dakaneye/word-clock-for-my-daughters/docs/superpowers/plans/2026-07-13-sd-loader.md

# SD Loader Implementation Plan

> **For agentic workers:** REQUIRED SUB-SKILL: Use superpowers:subagent-driven-development (recommended) or superpowers:executing-plans to implement this plan task-by-task. Steps use checkbox (`- [ ]`) syntax for tracking.

**Goal:** One command that loads/updates the three audio WAVs on the SD card inside a closed clock over the captive USB cable + WiFi, then restores the exact firmware image that was running.

**Architecture:** A standalone loader firmware (`firmware/tools/sd_loader/`) mounts the SD, joins WiFi (NVS creds or serial-supplied), and executes line-based serial commands to pull files from a temporary HTTP server on the Mac. A host orchestrator (`firmware/tools/sd_load.py`) stages/converts audio, dumps the clock's full flash with esptool, flashes the loader, drives the transfer, then writes the dump back. Pure logic lives in `sd_load_core.py` (pytest-covered, importable without pyserial/esptool).

**Tech Stack:** PlatformIO (espressif32@6.8.0, Arduino), Python 3 stdlib (+pyserial), esptool (PlatformIO-bundled 4.5), afconvert (macOS built-in).

**Spec:** `docs/superpowers/specs/2026-07-13-sd-loader-design.md`

## Global Constraints

- Loader firmware pins `platform = espressif32@6.8.0` (exact, no caret) and `build_unflags = -std=gnu++11` — both load-bearing (CLAUDE.md).
- `board = esp32dev`, `monitor_speed = 115200`, serial protocol at 115200.
- Canonical SD filenames: `lullaby1.wav`, `lullaby2.wav`, `birth.wav` at FAT32 root. WAV format: RIFF/WAVE, PCM (format 1), mono, 44100 Hz, 16-bit.
- CRC32 = zlib polynomial (0xEDB88320), init 0, both sides.
- Serial protocol fields are TAB-separated (SSIDs/passwords may contain spaces).
- pio at `~/Library/Python/3.9/bin/pio`; esptool at `~/.platformio/packages/tool-esptoolpy/esptool.py`.
- Conventional commits, no attribution trailers. All commands below run from `firmware/`.
- The clone CP2102 replays stale serial data: every fresh capture uses reset-hold → flush → release (see `tools/bench_acceptance.py` `Board.reset_and_capture`).

---

### Task 1: Host pure-logic core

**Files:**
- Create: `firmware/tools/sd_load_core.py`
- Test: `firmware/tools/test_sd_load_core.py`

**Interfaces:**
- Produces (used by Task 3):
  - `validate_wav(path: Path) -> int` — returns data-chunk byte size; raises `ValueError` with a human reason on any spec violation
  - `file_crc32(path: Path) -> int`
  - `afconvert_cmd(src: Path, dst: Path) -> list[str]`
  - `resolve_inputs(args) -> dict[str, Path]` — maps slot name (`lullaby1.wav` etc.) → source file; raises `ValueError` if nothing resolves
  - `format_get(url: str, name: str, size: int, crc: int) -> str` — the `G` line
  - `parse_line(line: str) -> dict` — `{"kind": "ready"|"ok"|"err"|"file"|"prog"|"noise", ...fields}`
  - `backup_name(now: datetime) -> str` — `flash-YYYYMMDD-HHMMSS.bin`

- [ ] **Step 1: Write the failing tests**

```python
# firmware/tools/test_sd_load_core.py
import struct
import zlib
from datetime import datetime
from pathlib import Path

import pytest

import sd_load_core as core

def make_wav(path: Path, *, channels=1, rate=44100, bits=16,
             fmt=1, data=b"\x00\x01" * 100, magic=b"RIFF", wave=b"WAVE"):
    """Minimal RIFF/WAVE writer for tests."""
    fmt_chunk = struct.pack("<4sIHHIIHH", b"fmt ", 16, fmt, channels,
                            rate, rate * channels * bits // 8,
                            channels * bits // 8, bits)
    data_chunk = struct.pack("<4sI", b"data", len(data)) + data
    body = wave + fmt_chunk + data_chunk
    path.write_bytes(magic + struct.pack("<I", len(body)) + body)
    return path

def test_validate_wav_accepts_spec_file(tmp_path):
    p = make_wav(tmp_path / "ok.wav")
    assert core.validate_wav(p) == 200

@pytest.mark.parametrize("kwargs,needle", [
    ({"channels": 2}, "mono"),
    ({"rate": 48000}, "44100"),
    ({"bits": 24}, "16-bit"),
    ({"fmt": 3}, "PCM"),
    ({"magic": b"RIFX"}, "RIFF"),
    ({"data": b""}, "empty"),
])
def test_validate_wav_rejects_violations(tmp_path, kwargs, needle):
    p = make_wav(tmp_path / "bad.wav", **kwargs)
    with pytest.raises(ValueError, match=needle):
        core.validate_wav(p)

def test_file_crc32_matches_zlib(tmp_path):
    p = tmp_path / "f.bin"
    p.write_bytes(b"hello sd loader")
    assert core.file_crc32(p) == zlib.crc32(b"hello sd loader")

def test_afconvert_cmd_shape(tmp_path):
    cmd = core.afconvert_cmd(Path("in.m4a"), Path("out.wav"))
    assert cmd[0] == "afconvert"
    assert "-d" in cmd and "LEI16@44100" in cmd
    assert "-c" in cmd and "1" in cmd
    assert cmd[-2:] == ["in.m4a", "out.wav"]

def test_resolve_inputs_from_flags(tmp_path):
    a = make_wav(tmp_path / "a.wav")
    got = core.resolve_inputs(
        type("A", (), {"lullaby1": a, "lullaby2": None, "birth": None,
                       "directory": None})())
    assert got == {"lullaby1.wav": a}

def test_resolve_inputs_from_directory(tmp_path):
    l1 = make_wav(tmp_path / "lullaby1.m4a")
    b = make_wav(tmp_path / "birth.wav")
    got = core.resolve_inputs(
        type("A", (), {"lullaby1": None, "lullaby2": None, "birth": None,
                       "directory": tmp_path})())
    assert got == {"lullaby1.wav": l1, "birth.wav": b}

def test_resolve_inputs_empty_raises(tmp_path):
    with pytest.raises(ValueError, match="[Nn]o input"):
        core.resolve_inputs(
            type("A", (), {"lullaby1": None, "lullaby2": None,
                           "birth": None, "directory": tmp_path})())

def test_format_get_is_tab_separated():
    line = core.format_get("http://10.0.0.5:8123/birth.wav",
                           "birth.wav", 12345, 0xDEADBEEF)
    assert line == ("G http://10.0.0.5:8123/birth.wav\tbirth.wav"
                    "\t12345\tdeadbeef\n")

@pytest.mark.parametrize("line,kind,extra", [
    ("READY sd=ok wifi=192.168.1.44", "ready",
     {"sd": "ok", "wifi": "192.168.1.44"}),
    ("READY sd=fail wifi=none", "ready", {"sd": "fail", "wifi": "none"}),
    ("OK got birth.wav 12345 deadbeef", "ok", {}),
    ("ERR get http 404", "err", {}),
    ("FILE lullaby1.wav 10485760 0012abcd", "file",
     {"name": "lullaby1.wav", "size": 10485760, "crc": 0x0012ABCD}),
    ("PROG birth.wav 45", "prog", {"name": "birth.wav", "pct": 45}),
    ("[boot] anything else", "noise", {}),
])
def test_parse_line(line, kind, extra):
    got = core.parse_line(line)
    assert got["kind"] == kind
    for k, v in extra.items():
        assert got[k] == v

def test_backup_name():
    assert core.backup_name(datetime(2026, 7, 13, 9, 5, 7)) == \
        "flash-20260713-090507.bin"
```

- [ ] **Step 2: Run tests to verify they fail**

Run: `cd firmware/tools && python3 -m pytest test_sd_load_core.py -q`
Expected: collection error — `ModuleNotFoundError: No module named 'sd_load_core'`

- [ ] **Step 3: Write the implementation**

```python
# firmware/tools/sd_load_core.py
"""Pure logic for sd_load.py — importable without pyserial/esptool.

WAV validation, CRC, input resolution, and the serial protocol's line
formats. The wire protocol is defined in
docs/superpowers/specs/2026-07-13-sd-loader-design.md.
"""
import re
import struct
import zlib
from datetime import datetime
from pathlib import Path

SLOTS = ("lullaby1.wav", "lullaby2.wav", "birth.wav")

def validate_wav(path: Path) -> int:
    """Return the data-chunk size of a spec-compliant WAV; raise
    ValueError naming the first violation. Spec: RIFF/WAVE, PCM,
    mono, 44100 Hz, 16-bit, non-empty data."""
    raw = Path(path).read_bytes()
    if len(raw) < 44 or raw[0:4] != b"RIFF" or raw[8:12] != b"WAVE":
        raise ValueError(f"{path.name}: not a RIFF/WAVE file")
    pos, fmt_seen, data_size = 12, False, None
    while pos + 8 <= len(raw):
        cid, csize = raw[pos:pos + 4], struct.unpack_from("<I", raw, pos + 4)[0]
        body = raw[pos + 8:pos + 8 + csize]
        if cid == b"fmt ":
            fmt_seen = True
            fmt, ch, rate, _, _, bits = struct.unpack_from("<HHIIHH", body)
            if fmt != 1:
                raise ValueError(f"{path.name}: not PCM (format {fmt})")
            if ch != 1:
                raise ValueError(f"{path.name}: {ch} channels — must be mono")
            if rate != 44100:
                raise ValueError(f"{path.name}: {rate} Hz — must be 44100")
            if bits != 16:
                raise ValueError(f"{path.name}: {bits}-bit — must be 16-bit")
        elif cid == b"data":
            data_size = csize
        pos += 8 + csize + (csize & 1)   # chunks are word-aligned
    if not fmt_seen:
        raise ValueError(f"{path.name}: missing fmt chunk")
    if not data_size:
        raise ValueError(f"{path.name}: empty data chunk")
    return data_size

def file_crc32(path: Path) -> int:
    crc = 0
    with open(path, "rb") as f:
        while chunk := f.read(65536):
            crc = zlib.crc32(chunk, crc)
    return crc

def afconvert_cmd(src: Path, dst: Path) -> list:
    return ["afconvert", "-f", "WAVE", "-d", "LEI16@44100", "-c", "1",
            str(src), str(dst)]

def resolve_inputs(args) -> dict:
    """Map canonical slot names to source paths from --lullaby1/2/--birth
    flags or a directory of files named <slot-stem>.*  (≥1 required)."""
    out = {}
    for slot in SLOTS:
        stem = slot.split(".")[0]           # lullaby1 / lullaby2 / birth
        flag = getattr(args, stem, None)
        if flag:
            out[slot] = Path(flag)
    if not out and getattr(args, "directory", None):
        d = Path(args.directory)
        for slot in SLOTS:
            stem = slot.split(".")[0]
            hits = sorted(d.glob(f"{stem}.*"))
            if hits:
                out[slot] = hits[0]
    if not out:
        raise ValueError(
            "no inputs: pass --lullaby1/--lullaby2/--birth or a directory "
            f"containing files named {', '.join(s.split('.')[0] + '.*' for s in SLOTS)}")
    return out

def format_get(url: str, name: str, size: int, crc: int) -> str:
    return f"G {url}\t{name}\t{size}\t{crc:08x}\n"

_READY = re.compile(r"^READY sd=(\w+) wifi=(\S+)$")
_FILE = re.compile(r"^FILE (\S+) (\d+) ([0-9a-fA-F]{8})$")
_PROG = re.compile(r"^PROG (\S+) (\d+)$")

def parse_line(line: str) -> dict:
    line = line.strip()
    if m := _READY.match(line):
        return {"kind": "ready", "sd": m.group(1), "wifi": m.group(2)}
    if line.startswith("OK "):
        return {"kind": "ok", "detail": line[3:]}
    if line.startswith("ERR "):
        return {"kind": "err", "detail": line[4:]}
    if m := _FILE.match(line):
        return {"kind": "file", "name": m.group(1),
                "size": int(m.group(2)), "crc": int(m.group(3), 16)}
    if m := _PROG.match(line):
        return {"kind": "prog", "name": m.group(1), "pct": int(m.group(2))}
    return {"kind": "noise", "detail": line}

def backup_name(now: datetime) -> str:
    return now.strftime("flash-%Y%m%d-%H%M%S.bin")
```

- [ ] **Step 4: Run tests to verify they pass**

Run: `cd firmware/tools && python3 -m pytest test_sd_load_core.py -q`
Expected: all pass.

- [ ] **Step 5: Commit**

```bash
git add tools/sd_load_core.py tools/test_sd_load_core.py
git commit -m "feat(tools): sd loader host core logic"
```

---

### Task 2: Loader firmware

**Files:**
- Create: `firmware/tools/sd_loader/platformio.ini`
- Create: `firmware/tools/sd_loader/src/main.cpp`

**Interfaces:**
- Consumes: `configs/pinmap.h` (`PIN_SD_CS`), NVS namespace `wifi`
  (`ssid`/`pw`/`valid` keys — same schema as `nvs_store.cpp`)
- Produces: the serial protocol Task 3 drives (`READY`/`OK`/`ERR`/`FILE`/`PROG` lines; `W`/`G`/`L`/`D` commands per the spec)

- [ ] **Step 1: Write `platformio.ini`**

```ini
; firmware/tools/sd_loader/platformio.ini
; Standalone loader project — see
; docs/superpowers/specs/2026-07-13-sd-loader-design.md.
; Platform pin + build_unflags are load-bearing (CLAUDE.md): 6.8.0 exact,
; and Arduino-ESP32 appends -std=gnu++11 after ours without the unflag.
[env:sdloader]
platform = espressif32@6.8.0
framework = arduino
board = esp32dev
monitor_speed = 115200
build_unflags = -std=gnu++11
build_flags =
    -std=gnu++17
    -Wall
    -Wextra
    -I ../../configs
```

- [ ] **Step 2: Write the loader firmware**

```cpp
// firmware/tools/sd_loader/src/main.cpp
//
// SD LOADER — temporary firmware for cable-only SD content updates on a
// sealed clock. Flashed by tools/sd_load.py, which restores the original
// flash image afterwards. Serves line-based serial commands at 115200:
//
//   W <ssid>\t<pass>                join WiFi with explicit credentials
//   G <url>\t<name>\t<size>\t<crc>  download url -> /<name> (atomic)
//   L                               list SD root (name, size, crc32)
//   D <name>                        delete /<name>
//
// Protocol spec: docs/superpowers/specs/2026-07-13-sd-loader-design.md.
// Reads the clock's stored WiFi credentials from NVS (namespace "wifi",
// same schema as lib/wifi_provision/src/nvs_store.cpp). NEVER writes NVS.
#include <Arduino.h>
#include <HTTPClient.h>
#include <Preferences.h>
#include <SD.h>
#include <WiFi.h>
#include "pinmap.h"

static bool sd_ok = false;

// ---- CRC32 (zlib polynomial, init 0) --------------------------------
static uint32_t crc_table[256];

static void crc_init() {
    for (uint32_t i = 0; i < 256; ++i) {
        uint32_t c = i;
        for (int k = 0; k < 8; ++k)
            c = (c & 1) ? (0xEDB88320UL ^ (c >> 1)) : (c >> 1);
        crc_table[i] = c;
    }
}

// zlib-style: pass the previous return value back in (start with 0).
static uint32_t crc_update(uint32_t crc, const uint8_t* buf, size_t len) {
    crc ^= 0xFFFFFFFFUL;
    for (size_t i = 0; i < len; ++i)
        crc = crc_table[(crc ^ buf[i]) & 0xFF] ^ (crc >> 8);
    return crc ^ 0xFFFFFFFFUL;
}

static uint32_t crc_of_file(const char* path) {
    File f = SD.open(path, FILE_READ);
    if (!f) return 0;
    static uint8_t buf[4096];
    uint32_t crc = 0;
    while (true) {
        int n = f.read(buf, sizeof(buf));
        if (n <= 0) break;
        crc = crc_update(crc, buf, (size_t)n);
    }
    f.close();
    return crc;
}

// ---- WiFi ------------------------------------------------------------
static bool wifi_join(const String& ssid, const String& pw,
                      uint32_t timeout_ms = 20000) {
    WiFi.mode(WIFI_STA);
    WiFi.begin(ssid.c_str(), pw.c_str());
    uint32_t start = millis();
    while (WiFi.status() != WL_CONNECTED) {
        if (millis() - start > timeout_ms) return false;
        delay(100);
    }
    return true;
}

static bool wifi_from_nvs() {
    Preferences p;
    if (!p.begin("wifi", /*readOnly=*/true)) return false;
    bool valid = p.getUChar("valid", 0) == 1;
    String ssid = p.getString("ssid", "");
    String pw = p.getString("pw", "");
    p.end();
    if (!valid || ssid.isEmpty()) return false;
    return wifi_join(ssid, pw);
}

// ---- Commands --------------------------------------------------------
// Split a tab-separated tail into at most n parts (last part keeps tabs).
static int split_tabs(String tail, String* out, int n) {
    int count = 0;
    while (count < n - 1) {
        int t = tail.indexOf('\t');
        if (t < 0) break;
        out[count++] = tail.substring(0, t);
        tail = tail.substring(t + 1);
    }
    out[count++] = tail;
    return count;
}

static void cmd_get(const String& tail) {
    String part[4];
    if (split_tabs(tail, part, 4) != 4) {
        Serial.println("ERR get expected url\\tname\\tsize\\tcrc");
        return;
    }
    const String& url = part[0];
    const String name = "/" + part[1];
    const String temp = name + ".part";
    const uint32_t want_size = strtoul(part[2].c_str(), nullptr, 10);
    const uint32_t want_crc = strtoul(part[3].c_str(), nullptr, 16);

    if (WiFi.status() != WL_CONNECTED) {
        Serial.println("ERR get wifi not connected");
        return;
    }
    HTTPClient http;
    http.setTimeout(15000);
    if (!http.begin(url)) {
        Serial.println("ERR get bad url");
        return;
    }
    int code = http.GET();
    if (code != 200) {
        Serial.printf("ERR get http %d\n", code);
        http.end();
        return;
    }
    SD.remove(temp);
    File out = SD.open(temp, FILE_WRITE);
    if (!out) {
        Serial.println("ERR get sd open failed");
        http.end();
        return;
    }
    WiFiClient* stream = http.getStreamPtr();
    static uint8_t buf[4096];
    uint32_t got = 0, crc = 0, last_pct = 0;
    bool io_fail = false;
    while (got < want_size) {
        size_t want = min((uint32_t)sizeof(buf), want_size - got);
        int n = stream->readBytes(buf, want);   // blocks up to timeout
        if (n <= 0) break;                       // stalled / closed early
        if (out.write(buf, (size_t)n) != (size_t)n) {
            io_fail = true;
            break;
        }
        crc = crc_update(crc, buf, (size_t)n);
        got += (uint32_t)n;
        uint32_t pct = (uint32_t)((uint64_t)got * 100 / want_size);
        if (pct >= last_pct + 5) {
            Serial.printf("PROG %s %u\n", part[1].c_str(), (unsigned)pct);
            last_pct = pct;
        }
    }
    out.close();
    http.end();
    if (io_fail || got != want_size) {
        SD.remove(temp);
        Serial.printf("ERR get short transfer %u/%u%s\n", (unsigned)got,
                      (unsigned)want_size, io_fail ? " (sd write)" : "");
        return;
    }
    if (crc != want_crc) {
        SD.remove(temp);
        Serial.println("ERR get stream crc mismatch");
        return;
    }
    // Read back from the card — proves the bytes that LANDED are right.
    uint32_t disk_crc = crc_of_file(temp.c_str());
    if (disk_crc != want_crc) {
        SD.remove(temp);
        Serial.println("ERR get readback crc mismatch");
        return;
    }
    SD.remove(name);
    if (!SD.rename(temp, name)) {
        Serial.println("ERR get rename failed");
        return;
    }
    Serial.printf("OK got %s %u %08x\n", part[1].c_str(),
                  (unsigned)want_size, (unsigned)want_crc);
}

static void cmd_list() {
    File root = SD.open("/");
    if (!root) {
        Serial.println("ERR list sd root");
        return;
    }
    for (File f = root.openNextFile(); f; f = root.openNextFile()) {
        if (!f.isDirectory()) {
            String path = String("/") + f.name();
            uint32_t size = f.size();
            f.close();
            Serial.printf("FILE %s %u %08x\n", path.c_str() + 1,
                          (unsigned)size,
                          (unsigned)crc_of_file(path.c_str()));
        } else {
            f.close();
        }
    }
    root.close();
    Serial.println("OK list");
}

static void handle(const String& line) {
    if (line.startsWith("W ")) {
        String part[2];
        if (split_tabs(line.substring(2), part, 2) != 2) {
            Serial.println("ERR wifi expected ssid\\tpass");
        } else if (wifi_join(part[0], part[1])) {
            Serial.printf("OK wifi %s\n", WiFi.localIP().toString().c_str());
        } else {
            Serial.println("ERR wifi join failed");
        }
    } else if (line.startsWith("G ")) {
        cmd_get(line.substring(2));
    } else if (line == "L") {
        cmd_list();
    } else if (line.startsWith("D ")) {
        String name = "/" + line.substring(2);
        if (SD.remove(name)) Serial.printf("OK del %s\n", name.c_str() + 1);
        else Serial.printf("ERR del %s\n", name.c_str() + 1);
    } else if (line.length() > 0) {
        Serial.println("ERR unknown command");
    }
}

void setup() {
    Serial.begin(115200);
    crc_init();
    sd_ok = SD.begin(PIN_SD_CS);
    bool wifi = wifi_from_nvs();
    Serial.printf("READY sd=%s wifi=%s\n", sd_ok ? "ok" : "fail",
                  wifi ? WiFi.localIP().toString().c_str() : "none");
}

void loop() {
    static String line;
    while (Serial.available()) {
        char c = (char)Serial.read();
        if (c == '\n') {
            line.trim();
            handle(line);
            line = "";
        } else {
            line += c;
        }
    }
    delay(2);
}
```

- [ ] **Step 3: Compile**

Run: `~/Library/Python/3.9/bin/pio run -d tools/sd_loader`
Expected: `[SUCCESS]`. If `pinmap.h` is not found, the include path is
wrong — it must resolve `firmware/configs/` from `firmware/tools/sd_loader/`
(`-I ../../configs`).

- [ ] **Step 4: Add the build directory to gitignore**

Append to the repo root `.gitignore`:

```
firmware/tools/sd_loader/.pio/
firmware/tools/.flash_backups/
```

- [ ] **Step 5: Commit**

```bash
git add tools/sd_loader/platformio.ini tools/sd_loader/src/main.cpp ../.gitignore
git commit -m "feat(tools): sd loader firmware"
```

---

### Task 3: Host orchestrator

**Files:**
- Create: `firmware/tools/sd_load.py`

**Interfaces:**
- Consumes (from Task 1): `validate_wav`, `file_crc32`, `afconvert_cmd`, `resolve_inputs`, `format_get`, `parse_line`, `backup_name`, `SLOTS`
- Consumes (from Task 2): the loader serial protocol
- Produces: the user-facing command (`sd_load.py [dir] [--lullaby1/--lullaby2/--birth] [--dry-run] [--restore-only BIN] [--port]`)

- [ ] **Step 1: Write the orchestrator**

```python
#!/usr/bin/env python3
"""Load/update the clock's SD audio over the captive USB cable.

Stages (each a hard gate, all narrated):
  1 stage    convert inputs to spec WAVs (afconvert), validate, CRC
  2 backup   esptool read_flash of the ENTIRE flash to tools/.flash_backups/
  3 load     flash the loader firmware, serve staged files over HTTP,
             drive the serial protocol until every CRC matches
  4 restore  esptool write_flash the backup back, verify boot markers

If anything fails after the loader is flashed, the tool attempts the
restore automatically and, failing that, prints the exact
--restore-only recovery command. Design:
docs/superpowers/specs/2026-07-13-sd-loader-design.md
"""
import argparse
import functools
import http.server
import math
import re
import shutil
import socket
import struct
import subprocess
import sys
import tempfile
import threading
import time
import wave
from datetime import datetime, timezone
from pathlib import Path

import serial

import sd_load_core as core

TOOLS = Path(__file__).resolve().parent
FIRMWARE = TOOLS.parent
LOADER = TOOLS / "sd_loader"
BACKUPS = TOOLS / ".flash_backups"
PIO = Path.home() / "Library/Python/3.9/bin/pio"
ESPTOOL = Path.home() / ".platformio/packages/tool-esptoolpy/esptool.py"
BAUDS = (921600, 460800, 115200)
PORT_DEFAULT = "/dev/cu.usbserial-0001"

def say(msg):
    print(f"== {msg}", flush=True)

def run(cmd, **kw):
    print(f"   $ {' '.join(str(c) for c in cmd)}", flush=True)
    return subprocess.run([str(c) for c in cmd], check=True, **kw)

def esptool(port, args, capture=False):
    """Run esptool with baud fallback (clone CP2102 flakes at high baud)."""
    last = None
    for baud in BAUDS:
        cmd = ["python3", ESPTOOL, "--port", port, "--baud", str(baud)] + args
        try:
            return run(cmd, capture_output=capture, text=True)
        except subprocess.CalledProcessError as e:
            last = e
            say(f"esptool failed at {baud} baud; retrying slower")
    raise last

def detect_flash_size(port) -> int:
    out = esptool(port, ["flash_id"], capture=True).stdout
    m = re.search(r"Detected flash size: (\d+)MB", out)
    if not m:
        raise RuntimeError(f"could not detect flash size:\n{out}")
    return int(m.group(1)) * 1024 * 1024

def lan_ip() -> str:
    s = socket.socket(socket.AF_INET, socket.SOCK_DGRAM)
    s.connect(("8.8.8.8", 80))          # no packets sent; picks the LAN iface
    ip = s.getsockname()[0]
    s.close()
    return ip

class Clock:
    """Serial session against the loader (or clock) with the replay-safe
    reset recipe — the clone CP2102 re-delivers stale buffers."""

    def __init__(self, port):
        self.s = serial.Serial()
        self.s.port = port
        self.s.baudrate = 115200
        self.s.timeout = 1.0
        self.s.dtr = False
        self.s.rts = False
        self.s.open()

    def reset(self):
        self.s.rts = True
        deadline = time.time() + 1.5
        while time.time() < deadline:
            self.s.reset_input_buffer()
            time.sleep(0.1)
        self.s.rts = False

    def lines(self, seconds):
        start, last = time.time(), None
        while time.time() - start < seconds:
            raw = self.s.readline()
            if not raw:
                continue
            text = raw.decode("utf-8", errors="replace").strip()
            if text and text != last:
                last = text
                yield text

    def command(self, line, timeout=120):
        """Send one command; stream PROG lines; return the OK/ERR parse."""
        self.s.write(line.encode() if line.endswith("\n")
                     else (line + "\n").encode())
        self.s.flush()
        for text in self.lines(timeout):
            p = core.parse_line(text)
            if p["kind"] == "prog":
                print(f"   ... {p['name']} {p['pct']}%", flush=True)
            elif p["kind"] in ("ok", "err"):
                return p
            elif p["kind"] == "file":
                print(f"   {p['name']:<16} {p['size']:>9}  crc {p['crc']:08x}",
                      flush=True)
        return {"kind": "err", "detail": f"timeout waiting for reply to {line!r}"}

    def close(self):
        self.s.close()

def make_test_wav(path: Path):
    """100 KB 440 Hz test tone, spec format, for --dry-run."""
    with wave.open(str(path), "wb") as w:
        w.setnchannels(1)
        w.setsampwidth(2)
        w.setframerate(44100)
        n = 50_000
        frames = b"".join(
            struct.pack("<h", int(12000 * math.sin(
                2 * math.pi * 440 * i / 44100))) for i in range(n))
        w.writeframes(frames)

def stage(args, staging: Path) -> dict:
    say("stage: converting + validating inputs")
    plan = {}
    if args.dry_run:
        p = staging / "dryrun.tmp"
        make_test_wav(p)
        plan["dryrun.tmp"] = p
    else:
        for slot, src in core.resolve_inputs(args).items():
            dst = staging / slot
            if src.suffix.lower() == ".wav":
                shutil.copy(src, dst)
            else:
                run(core.afconvert_cmd(src, dst))
            core.validate_wav(dst)
            plan[slot] = dst
    for name, p in plan.items():
        print(f"   {name:<16} {p.stat().st_size:>9} bytes  "
              f"crc {core.file_crc32(p):08x}")
    return plan

def transfer(clock: Clock, plan: dict, ip: str, port: int):
    for name, path in plan.items():
        size, crc = path.stat().st_size, core.file_crc32(path)
        url = f"http://{ip}:{port}/{path.name}"
        say(f"load: {name} ({size} bytes)")
        for attempt in range(3):
            reply = clock.command(core.format_get(url, name, size, crc))
            if reply["kind"] == "ok":
                break
            say(f"retry {attempt + 1}/3: {reply['detail']}")
        else:
            raise RuntimeError(f"transfer failed for {name}")
    if "dryrun.tmp" in plan:
        say("dry run: deleting test file")
        reply = clock.command("D dryrun.tmp", timeout=30)
        if reply["kind"] != "ok":
            raise RuntimeError(f"dry-run cleanup failed: {reply['detail']}")
    say("card contents after load:")
    clock.command("L", timeout=300)

def boot_check(port) -> bool:
    say("boot check: capturing restored firmware boot")
    clock = Clock(port)
    try:
        clock.reset()
        seen = set()
        for text in clock.lines(30):
            print(f"   | {text}")
            if "word-clock booting" in text:
                seen.add("banner")
            if "[boot] audio::begin done" in text:
                seen.add("setup")
            if "[bench] frame" in text or "-> Online" in text:
                seen.add("alive")
                break
        return {"banner", "setup"} <= seen
    finally:
        clock.close()

def main():
    ap = argparse.ArgumentParser(description=__doc__)
    ap.add_argument("directory", nargs="?", help="dir with lullaby1.*/lullaby2.*/birth.*")
    ap.add_argument("--lullaby1")
    ap.add_argument("--lullaby2")
    ap.add_argument("--birth")
    ap.add_argument("--dry-run", action="store_true")
    ap.add_argument("--restore-only", metavar="BACKUP_BIN")
    ap.add_argument("--port", default=PORT_DEFAULT)
    ap.add_argument("--wifi-ssid", help="explicit WiFi for an unprovisioned "
                    "board (sent to the loader as a W command)")
    ap.add_argument("--wifi-pass", default="")
    args = ap.parse_args()

    BACKUPS.mkdir(exist_ok=True)

    if args.restore_only:
        say(f"restore-only from {args.restore_only}")
        esptool(args.port, ["write_flash", "0x0", args.restore_only])
        sys.exit(0 if boot_check(args.port) else 1)

    staging = Path(tempfile.mkdtemp(prefix="sdload-"))
    plan = stage(args, staging)

    say("backup: reading full flash image")
    size = detect_flash_size(args.port)
    backup = BACKUPS / core.backup_name(datetime.now(timezone.utc))
    esptool(args.port, ["read_flash", "0", hex(size), str(backup)])
    say(f"backup saved: {backup} ({backup.stat().st_size} bytes)")

    loader_flashed = False
    try:
        say("load: flashing loader firmware")
        run([PIO, "run", "-d", LOADER, "-t", "upload",
             "--upload-port", args.port])
        loader_flashed = True

        handler = functools.partial(
            http.server.SimpleHTTPRequestHandler, directory=str(staging))
        httpd = http.server.ThreadingHTTPServer(("0.0.0.0", 0), handler)
        threading.Thread(target=httpd.serve_forever, daemon=True).start()
        ip, http_port = lan_ip(), httpd.server_address[1]
        say(f"serving staged files at http://{ip}:{http_port}/")

        clock = Clock(args.port)
        try:
            clock.reset()
            ready = None
            for text in clock.lines(25):
                p = core.parse_line(text)
                if p["kind"] == "ready":
                    ready = p
                    break
            if not ready:
                raise RuntimeError("loader never printed READY")
            if ready["sd"] != "ok":
                raise RuntimeError("loader could not mount the SD card")
            if not re.match(r"\d+\.\d+\.\d+\.\d+", ready["wifi"]):
                if not args.wifi_ssid:
                    raise RuntimeError(
                        "loader has no WiFi (NVS empty?) — pass "
                        "--wifi-ssid/--wifi-pass for an unprovisioned board")
                say(f"wifi: joining {args.wifi_ssid} via W command")
                reply = clock.command(
                    f"W {args.wifi_ssid}\t{args.wifi_pass}", timeout=30)
                if reply["kind"] != "ok":
                    raise RuntimeError(f"loader WiFi join failed: "
                                       f"{reply['detail']}")
            transfer(clock, plan, ip, http_port)
        finally:
            clock.close()
            httpd.shutdown()
    finally:
        if loader_flashed:
            say("restore: writing original flash image back")
            try:
                esptool(args.port, ["write_flash", "0x0", str(backup)])
            except Exception:
                say("RESTORE FAILED — recover with:")
                say(f"  python3 tools/sd_load.py --restore-only {backup} "
                    f"--port {args.port}")
                raise

    ok = boot_check(args.port)
    say("SUCCESS — clock restored and healthy" if ok else
        f"restore wrote OK but boot check failed; backup at {backup}")
    sys.exit(0 if ok else 1)

if __name__ == "__main__":
    main()
```

- [ ] **Step 2: Sanity gates**

Run: `cd firmware/tools && python3 -m pytest test_sd_load_core.py -q`
Expected: still all pass.

Run: `cd firmware/tools && python3 sd_load.py --help`
Expected: usage text, exit 0.

Run: `cd firmware/tools && python3 -c "import ast; ast.parse(open('sd_load.py').read())"`
Expected: no output (syntax valid).

- [ ] **Step 3: Commit**

```bash
git add tools/sd_load.py
git commit -m "feat(tools): sd loader host orchestrator"
```

---

### Task 4: Birthday playback for bench verification

**Files:**
- Modify: `firmware/lib/audio/include/audio.h` (after `play_lullaby()`)
- Modify: `firmware/lib/audio/src/audio.cpp` (next to `play_lullaby()`, ~line 320)
- Modify: `firmware/src/main.cpp` (BENCH_SIM command block)

**Interfaces:**
- Produces: `wc::audio::play_birthday_message()` and bench serial command `'b'`

- [ ] **Step 1: Add the API to `audio.h`** (after the `play_lullaby()` declaration)

```cpp
// Play birth.wav once, on demand. Same guards as play_lullaby(). Does
// NOT stamp the NVS birthday-year guard — that happens only in the
// auto-fire path — so a bench test never burns the real birthday.
void play_birthday_message();
```

- [ ] **Step 2: Add the implementation to `audio.cpp`** (immediately after `play_lullaby()`'s definition)

```cpp
void play_birthday_message() {
    if (!started || !sd_ok || !i2s_ok) return;
    dispatch_event(PlaybackEvent::Kind::BirthdayFired);
}
```

- [ ] **Step 3: Add the bench command in `main.cpp`** (after the `'l'` listing command in the BENCH_SIM block)

```cpp
        else if (c == 'b') {
            // Play birth.wav on demand (does not stamp the NVS birthday
            // guard) — audible verification after an SD reload.
            Serial.println("[bench] play birth.wav");
            wc::audio::play_birthday_message();
        }
```

- [ ] **Step 4: Build both targets + run native tests**

Run: `~/Library/Python/3.9/bin/pio run -e emory -e nora`
Expected: both `[SUCCESS]`.

Run: `~/Library/Python/3.9/bin/pio test -e native`
Expected: all pass (audio adapter is not in the native build; count unchanged).

- [ ] **Step 5: Commit** (includes the previously uncommitted `'l'` SD-listing bench command)

```bash
git add lib/audio/include/audio.h lib/audio/src/audio.cpp src/main.cpp
git commit -m "feat(audio): on-demand birthday playback + bench hooks"
```

---

### Task 5: Documentation

**Files:**
- Modify: `TODO.md` (Emory punch list)
- Modify: `docs/owners-manual.md` (Spare parts section)

- [ ] **Step 1: Update the TODO punch list**

In the Emory punch list, replace the line
`- [ ] Record real audio (parallel track below) and swap SD test files`
with:

```markdown
- [ ] Record real audio (parallel track below), then load it with
      `firmware/tools/sd_load.py` — cable-only, no screws (spec:
      docs/superpowers/specs/2026-07-13-sd-loader-design.md). HARD
      DEADLINE: before Oct 6 (first live birthday fire). Verify by ear:
      Audio button for lullabies, bench 'b' for birth.wav.
```

- [ ] **Step 2: Update the owner's manual**

In `docs/owners-manual.md` under "Spare parts and repairs", add after the coin-cell bullet:

```markdown
- **Re-recording the audio** never requires opening the clock: the
  recordings load over the USB cable using the loader tool in the
  project repository (`firmware/tools/sd_load.py`). The back only
  comes off for hardware — battery, or a physically failing card.
```

- [ ] **Step 3: Commit**

```bash
git add ../TODO.md ../docs/owners-manual.md
git commit -m "docs: sd loader usage and audio deadline"
```

---

### Task 6: Hardware acceptance (user-gated)

Requires the clock's captive cable plugged into the Mac. This is the
acceptance test for the entire pipeline and also produces the first real
listing of Emory's card.

- [ ] **Step 1: Dry run**

Run: `cd firmware/tools && python3 sd_load.py --dry-run --port /dev/cu.usbserial-0001`

Expected transcript shape:
```
== stage: converting + validating inputs
   dryrun.tmp          100044 bytes  crc ........
== backup: reading full flash image
== backup saved: .../flash-<ts>.bin (4194304 bytes)
== load: flashing loader firmware
== serving staged files at http://192.168.x.y:...
== load: dryrun.tmp (100044 bytes)
   ... dryrun.tmp 100%
== dry run: deleting test file
== card contents after load:
   lullaby1.wav  ...          <- finally see what's on Emory's card
== restore: writing original flash image back
== boot check: capturing restored firmware boot
== SUCCESS — clock restored and healthy
```

- [ ] **Step 2: Record the card listing** — paste the `FILE` lines into the
  session; update `TODO.md`'s audio item if `birth.wav` turns out to be
  absent vs. placeholder.

- [ ] **Step 3: Run the full bench acceptance suite** to prove the restore:

Run: `cd firmware && python3 tools/bench_acceptance.py`
Expected: `11/11 checks passed`.
