dakaneye/word-clock-for-my-daughters/docs/superpowers/plans/2026-04-14-daughters-clocks-implementation.md

# Daughters' Word Clocks Implementation Plan

> **For agentic workers:** REQUIRED SUB-SKILL: Use superpowers:subagent-driven-development (recommended) or superpowers:executing-plans to implement this plan task-by-task. Steps use checkbox (`- [ ]`) syntax for tracking.

**Goal:** Build two word clocks (Emory 2030, Nora 2032) on a shared ESP32 + WS2812B platform with per-kid compile-time configuration, matching the locked design spec at `docs/superpowers/specs/2026-04-14-daughters-clocks-design.md`.

**Architecture:** Single PlatformIO project with two build environments (`emory`, `nora`) that differ only by `-D CLOCK_TARGET=` flags pointing at `config_emory.h` / `config_nora.h`. Firmware is split into testable modules (time→words grid logic, color/animation, audio, WiFi/NTP, buttons, config). Native-host tests run the pure-logic modules (`time_to_words`, holiday date math, acrostic filler rendering) in CI without hardware. Hardware-dependent modules compile under the ESP32 env only. KiCad design files and 3D-printable internals live alongside firmware in the same repo. A single enclosure CAD and PCB footprint serve both units; wood species, dedication engraving, and per-kid config are the only diffs.

**Tech Stack:** PlatformIO + Arduino-ESP32 core, FastLED (WS2812B), ESP32 I2S + MAX98357A driver, NTPClient, RTClib (DS3231), Preferences (WiFi creds), KiCad 8.x, FreeCAD (or OpenSCAD) for 3D internals, Fusion 360 or Shaper Origin–friendly SVG for laser-cut wood faces. CI: GitHub Actions with `arduino/compile-sketches`-style PlatformIO build, Unity native tests, hookshot composite actions (`claude-review-code`, `gas-fixer`), release-pilot for tagging.

**Phase ordering rationale:** Repo+CI infra first (unblocks every future PR with linting, review, and vulnerability gates). Then native-testable firmware logic (grid → words, holidays, acrostic) — no hardware required, catches the highest-value bugs early. Then hardware bring-up on a breadboard to de-risk every IC *before* committing to a PCB. Then KiCad v1 using breadboard learnings. Then enclosure CAD against real PCB dimensions. Then integration + Emory unit 1 (prototype). Then Nora unit 2 with fixes baked in.

**Scope note:** Phases 0 and 1 are fully detailed below as executable TDD plans. Phases 2–6 are outlined with entry criteria, deliverables, and flagged open questions; each should get its own dedicated sub-plan (rerun `superpowers:writing-plans` against that phase's scope) when its entry criteria are met. Trying to fully plan a PCB in 2026 that won't be fabricated until ~2028 is a waste — the spec's "Open Items for Planning Phase" correctly defers those decisions.

## Amendments

- **2026-04-14 (execution day):** Dropped Tasks 0.5 (CodeQL), 0.6 (hookshot claude-review-code), 0.7 (hookshot gas-fixer), and 0.9 (trivy+gitleaks scan). Equivalent coverage is provided centrally by `dakaneye/.github` sync (settings.yml baseline ruleset + template workflows for CodeQL, security scan, and dependabot auto-merge). What used to be Task 0.10 (repo wrap-up + branch protection) is now Task 0.9 and reshaped into "trigger/verify org sync." Original task text below is left intact for historical reference but superseded — follow the current task list, not those sections.
- **2026-04-14:** Added a 3D-printing-fallback branch to Phase 4 (enclosure). If in-house printing (Bambu A1 purchase) isn't available when Phase 4 starts, outsource the internals via SendCutSend / Craftcloud / Shapeways. Budget impact: +$60-80/clock, still within the $150-180/clock spec target. See `docs/archive/specs/2026-04-14-3d-printer-purchase-decision.md` § Fallback.

---
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
