dakaneye/word-clock-for-my-daughters/firmware/tools/sd_load_core.py

"""Pure logic for sd_load.py — importable without pyserial/esptool.

WAV validation, CRC, input resolution, and the serial protocol's line
formats. The wire protocol is defined in
docs/superpowers/specs/2026-07-13-sd-loader-design.md.
"""
import re
import struct
import zlib
from datetime import datetime
from pathlib import Path

SLOTS = ("lullaby1.wav", "lullaby2.wav", "birth.wav")


def validate_wav(path: Path) -> int:
    """Return the data-chunk size of a spec-compliant WAV; raise
    ValueError naming the first violation. Spec: RIFF/WAVE, PCM,
    mono, 44100 Hz, 16-bit, non-empty data, and the canonical
    44-byte header layout — the clock firmware's parser
    (lib/audio/src/wav.cpp) requires the data chunk at offset 36
    and rejects anything else, so this validation must be exactly
    as strict."""
    raw = Path(path).read_bytes()
    if len(raw) < 44 or raw[0:4] != b"RIFF" or raw[8:12] != b"WAVE":
        raise ValueError(f"{path.name}: not a RIFF/WAVE file")
    pos, fmt_seen, data_size = 12, False, None
    while pos + 8 <= len(raw):
        cid, csize = raw[pos:pos + 4], struct.unpack_from("<I", raw, pos + 4)[0]
        body = raw[pos + 8:pos + 8 + csize]
        if cid == b"fmt ":
            if csize < 16:
                raise ValueError(f"{path.name}: truncated fmt chunk")
            fmt_seen = True
            fmt, ch, rate, _, _, bits = struct.unpack_from("<HHIIHH", body)
            if fmt != 1:
                raise ValueError(f"{path.name}: not PCM (format {fmt})")
            if ch != 1:
                raise ValueError(f"{path.name}: {ch} channels — must be mono")
            if rate != 44100:
                raise ValueError(f"{path.name}: {rate} Hz — must be 44100")
            if bits != 16:
                raise ValueError(f"{path.name}: {bits}-bit — must be 16-bit")
        elif cid == b"data":
            data_size = csize
        pos += 8 + csize + (csize & 1)   # chunks are word-aligned
    if not fmt_seen:
        raise ValueError(f"{path.name}: missing fmt chunk")
    if not data_size:
        raise ValueError(f"{path.name}: empty data chunk")
    if raw[36:40] != b"data":
        raise ValueError(
            f"{path.name}: data chunk not at offset 36 — not the canonical "
            "layout the clock firmware plays; run canonicalize_wav first")
    return data_size


def canonicalize_wav(path: Path) -> None:
    """Rewrite a WAV in place into the canonical 44-byte-header layout
    (fmt at 12, data at 36) the firmware parser requires. afconvert
    inserts a FLLR padding chunk between fmt and data, which the clock
    rejects as BadDataMagic. No-op if already canonical."""
    raw = Path(path).read_bytes()
    if len(raw) >= 44 and raw[0:4] == b"RIFF" and raw[8:12] == b"WAVE" \
            and raw[36:40] == b"data":
        return
    pos, fmt_body, data = 12, None, None
    while pos + 8 <= len(raw):
        cid, csize = raw[pos:pos + 4], struct.unpack_from("<I", raw, pos + 4)[0]
        if cid == b"fmt " and fmt_body is None:
            fmt_body = raw[pos + 8:pos + 8 + 16]
        elif cid == b"data" and data is None:
            data = raw[pos + 8:pos + 8 + csize]
        pos += 8 + csize + (csize & 1)   # chunks are word-aligned
    if fmt_body is None or len(fmt_body) < 16 or data is None:
        raise ValueError(f"{path.name}: cannot canonicalize — "
                         "missing fmt or data chunk")
    body = b"WAVE" + struct.pack("<4sI", b"fmt ", 16) + fmt_body \
        + struct.pack("<4sI", b"data", len(data)) + data
    Path(path).write_bytes(b"RIFF" + struct.pack("<I", len(body)) + body)


NORMALIZE_TARGET_PEAK = 29204   # -1 dBFS: 32767 * 10^(-1/20)


def normalize_wav_peak(path: Path) -> float:
    """Scale a canonical WAV in place so its loudest sample peaks at
    -1 dBFS, and return the gain factor applied. Voice-memo recordings
    land at unpredictable levels and the clock has no volume control,
    so staging brings every file to a consistent, full loudness. Never
    attenuates: files already at/above the target (or silent) are left
    byte-identical and 1.0 is returned."""
    raw = bytearray(Path(path).read_bytes())
    n = (len(raw) - 44) // 2
    samples = memoryview(raw)[44:44 + n * 2].cast("h")
    peak = 0
    for s in samples:
        a = -s if s < 0 else s
        if a > peak:
            peak = a
    if peak == 0 or peak >= NORMALIZE_TARGET_PEAK:
        return 1.0
    gain = NORMALIZE_TARGET_PEAK / peak
    for i in range(n):
        samples[i] = int(samples[i] * gain)   # |result| <= target < 32767
    samples.release()
    Path(path).write_bytes(bytes(raw))
    return gain


def file_crc32(path: Path) -> int:
    crc = 0
    with Path(path).open("rb") as f:
        while chunk := f.read(65536):
            crc = zlib.crc32(chunk, crc)
    return crc


def afconvert_cmd(src: Path, dst: Path) -> list:
    return ["afconvert", "-f", "WAVE", "-d", "LEI16@44100", "-c", "1",
            str(src), str(dst)]


def resolve_inputs(args) -> dict:
    """Map canonical slot names to source paths from --lullaby1/2/--birth
    flags or a directory of files named <slot-stem>.*  (≥1 required)."""
    out = {}
    for slot in SLOTS:
        stem = slot.split(".")[0]           # lullaby1 / lullaby2 / birth
        flag = getattr(args, stem, None)
        if flag:
            out[slot] = Path(flag)
    if not out and getattr(args, "directory", None):
        d = Path(args.directory)
        for slot in SLOTS:
            stem = slot.split(".")[0]
            hits = sorted(d.glob(f"{stem}.*"))
            if hits:
                out[slot] = hits[0]
    if not out:
        raise ValueError(
            "no inputs: pass --lullaby1/--lullaby2/--birth or a directory "
            f"containing files named {', '.join(s.split('.')[0] + '.*' for s in SLOTS)}")
    return out


def format_get(url: str, name: str, size: int, crc: int) -> str:
    return f"G {url}\t{name}\t{size}\t{crc:08x}\n"


_READY = re.compile(r"^READY sd=(\w+) wifi=(\S+)$")
_FILE = re.compile(r"^FILE (\S+) (\d+) ([0-9a-fA-F]{8})$")
_PROG = re.compile(r"^PROG (\S+) (\d+)$")
_OK_GOT = re.compile(r"^OK got (\S+) (\d+) ([0-9a-fA-F]{8})$")


def parse_line(line: str) -> dict:
    line = line.strip()
    if m := _READY.match(line):
        return {"kind": "ready", "sd": m.group(1), "wifi": m.group(2)}
    if m := _OK_GOT.match(line):
        return {"kind": "ok", "detail": line[3:],
                "got": {"name": m.group(1), "size": int(m.group(2)),
                        "crc": int(m.group(3), 16)}}
    if line.startswith("OK "):
        return {"kind": "ok", "detail": line[3:]}
    if line.startswith("ERR "):
        return {"kind": "err", "detail": line[4:]}
    if m := _FILE.match(line):
        return {"kind": "file", "name": m.group(1),
                "size": int(m.group(2)), "crc": int(m.group(3), 16)}
    if m := _PROG.match(line):
        return {"kind": "prog", "name": m.group(1), "pct": int(m.group(2))}
    return {"kind": "noise", "detail": line}


def got_matches(reply: dict, name: str, size: int, crc: int) -> bool:
    """True iff an OK reply's `got` payload matches the requested transfer.
    Defends the clone CP2102's stale-line replay: a replayed `OK got` from
    a previous file must never be accepted as this file's success."""
    got = reply.get("got")
    return bool(got) and got["name"] == name and got["size"] == size \
        and got["crc"] == crc


def validate_backup_image(path: Path, expected_size) -> None:
    """Refuse a flash backup that can't plausibly boot: exact size match
    (when the flash size is known; pass None otherwise) and the ESP32
    image magic 0xE9 at offset 0x1000, where the ROM expects the
    second-stage bootloader. A truncated or garbage backup written back
    would brick the clock."""
    actual = path.stat().st_size
    if expected_size is not None and actual != expected_size:
        raise ValueError(
            f"{path.name}: {actual} bytes, expected {expected_size} — "
            "backup is truncated or wrong; do not restore from it")
    with path.open("rb") as f:
        f.seek(0x1000)
        magic = f.read(1)
    if magic != b"\xe9":
        raise ValueError(
            f"{path.name}: no ESP32 bootloader magic at 0x1000 — "
            "not a flash image; do not restore from it")


def backup_name(now: datetime) -> str:
    return now.strftime("flash-%Y%m%d-%H%M%S.bin")
